pohjolaworks/Umo/STLs/Bottom/Bottom - bumpon mounts - kanji.stl

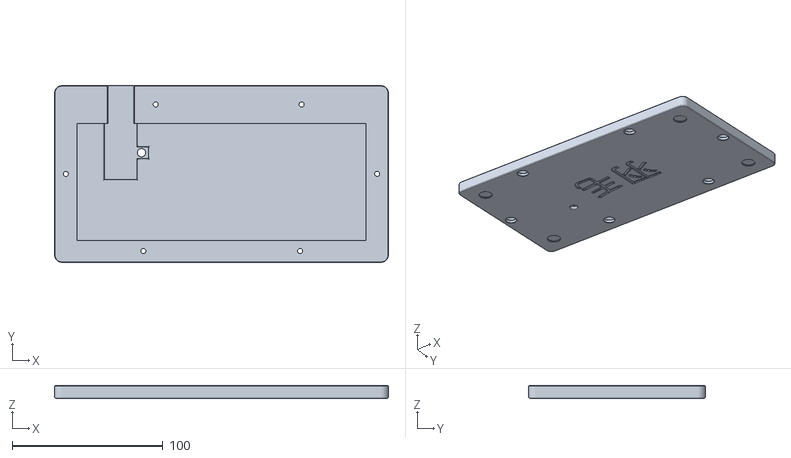
[picture p16: CAD file, 2021-05-14]
STLs/Bottom/Bottom - bumpon mounts - kanji.stl
221.5 x 117.2 x 8.50
