pohjolaworks/Umo/STLs/Plates/Universal.stl

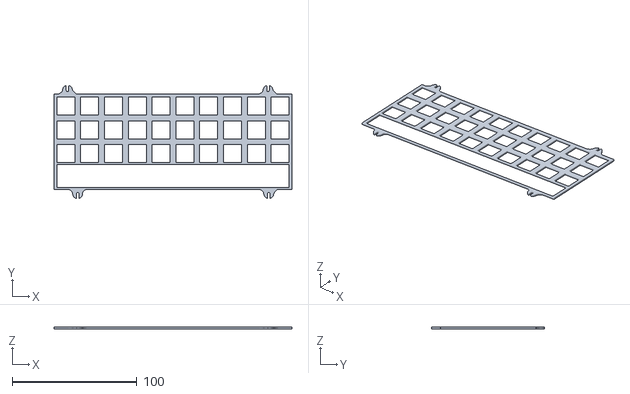
[picture p17: CAD file, 2021-05-14]
STLs/Plates/Universal.stl
190.5 x 90.3 x 1.50
