pohjolaworks/Umo/Plate files/1u Grid.dxf

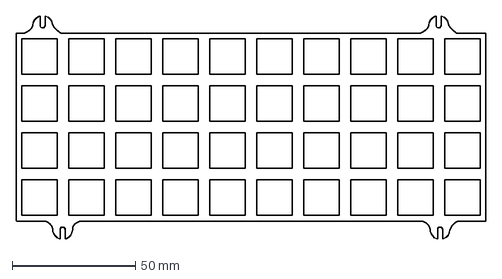
[picture p18: CAD file, 2021-05-21]
Plate files/1u Grid.dxf
190.5 x 90.3 mm
