pohjolaworks/Umo/Plate files/FR4/KiCAD Project/Universal.dxf

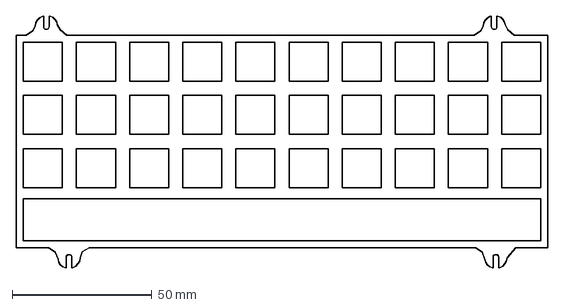
[picture p19: CAD file, 2021-05-22]
Plate files/FR4/KiCAD Project/Universal.dxf
190.5 x 90.3 mm
