pohjolaworks/Umo/STEPs/Other parts/Riser.step

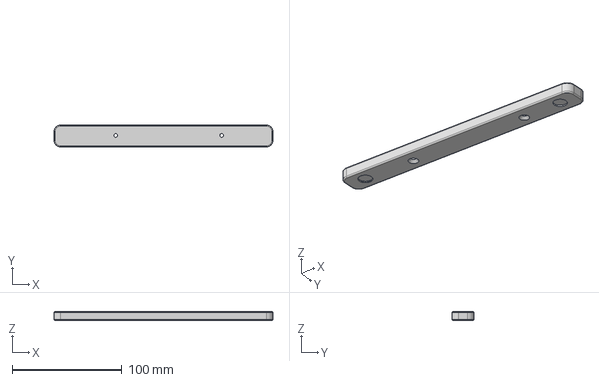
[picture p20: CAD file, 2024-12-05]
STEPs/Other parts/Riser.step
200.0 x 20.0 x 8.00 mm
