pohjolaworks/Umo/Plate files/Fixed 7u - 3mm.dxf

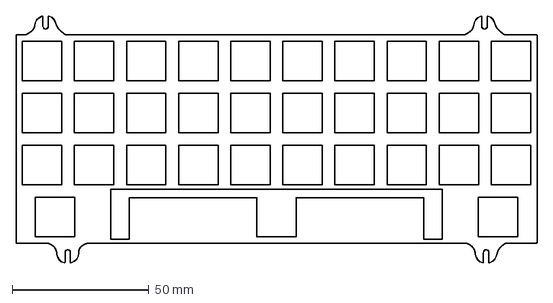
[picture p21: CAD file, 2021-05-21]
Plate files/Fixed 7u - 3mm.dxf
190.5 x 90.3 mm
