pohjolaworks/Umo/Plate files/FR4/KiCAD Project/Mounting point solder mask.dxf

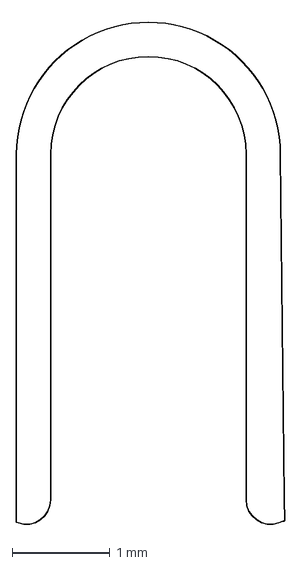
[picture p22: CAD file, 2021-05-22]
Plate files/FR4/KiCAD Project/Mounting point solder mask.dxf
2.75 x 5.21 mm
