pohjolaworks/Umo/STEPs/Plates/7U plate 1.5mm.step

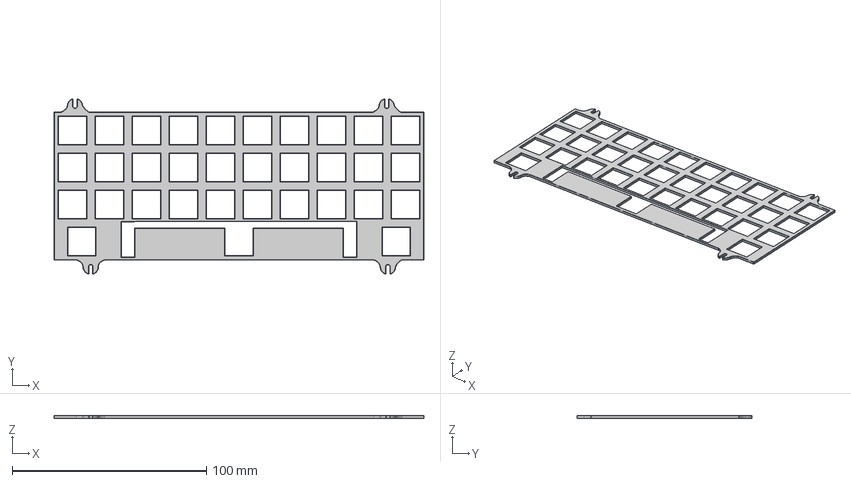
[picture p23: CAD file, 2024-12-05]
STEPs/Plates/7U plate 1.5mm.step
190.5 x 90.3 x 1.50 mm
