pohjolaworks/Umo/Plate files/2U or 2x 2U 3mm plate.dxf

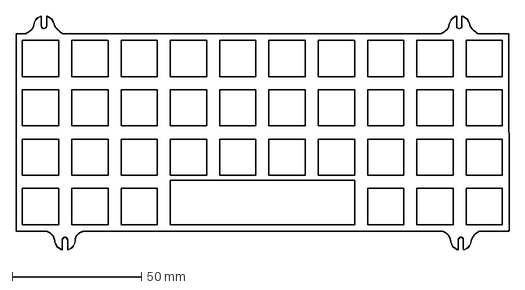
[picture p24: CAD file, 2021-05-21]
Plate files/2U or 2x 2U 3mm plate.dxf
190.5 x 90.3 mm
