pohjolaworks/Umo/Plate files/2x 2U.dxf

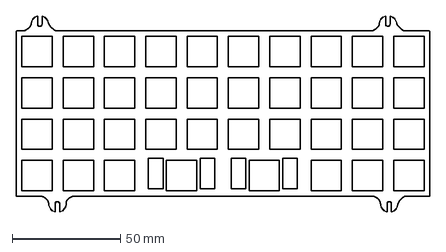
[picture p25: CAD file, 2021-05-21]
Plate files/2x 2U.dxf
190.5 x 90.3 mm
