pohjolaworks/Umo/Plate files/Fixed 7u.dxf

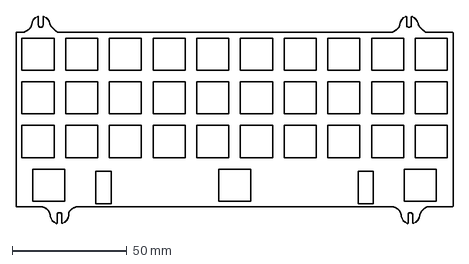
[picture p26: CAD file, 2021-05-21]
Plate files/Fixed 7u.dxf
190.5 x 90.3 mm
